icebreaker-fpga/icebreaker/hardware/bitsy-v1.0a/img/bare-ortho-bot_v1.0a.png

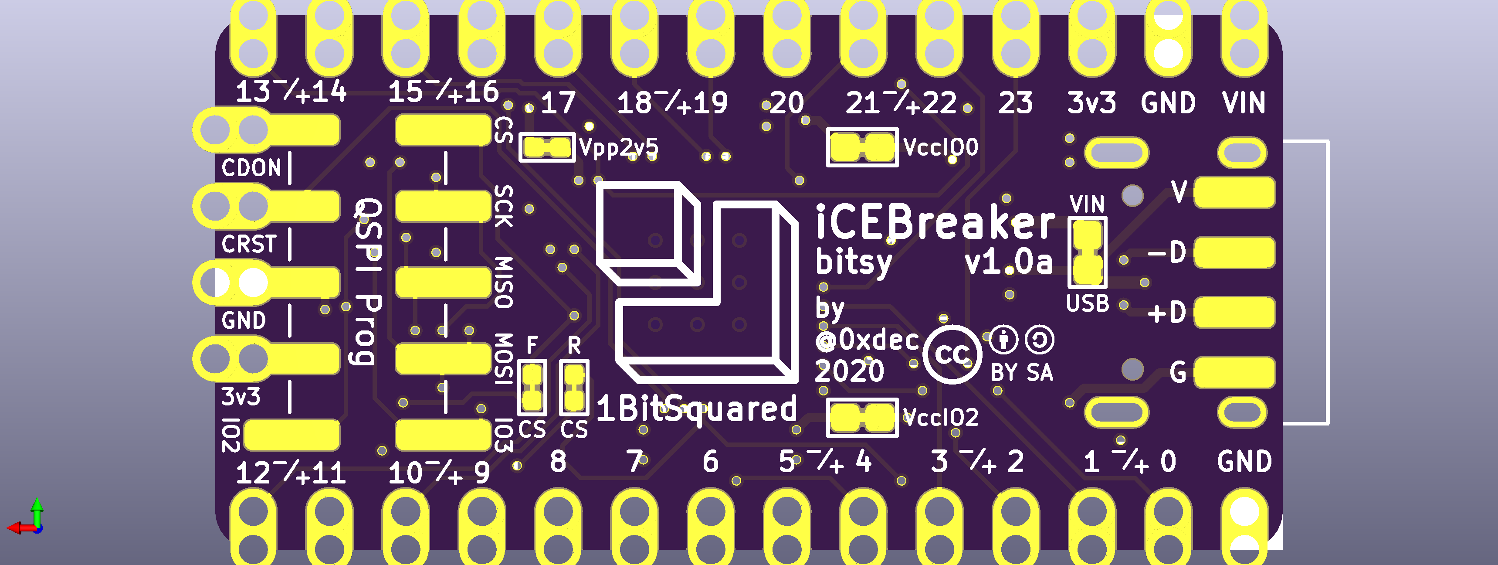
hardware/bitsy-v1.0a/img/bare-ortho-bot_v1.0a.png
