icebreaker-fpga/icebreaker/hardware/bitsy-v1.0a/img/bare-ortho-top_v1.0a.png

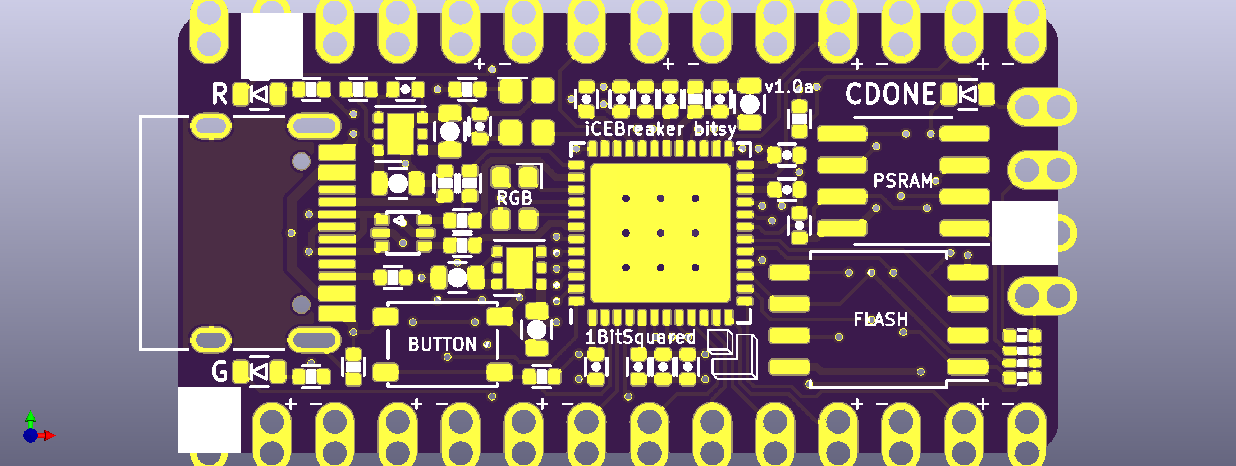
hardware/bitsy-v1.0a/img/bare-ortho-top_v1.0a.png
