icebreaker-fpga/icebreaker/hardware/bitsy-v1.1a/img/bitsy-v1.1a-info-card-top.png

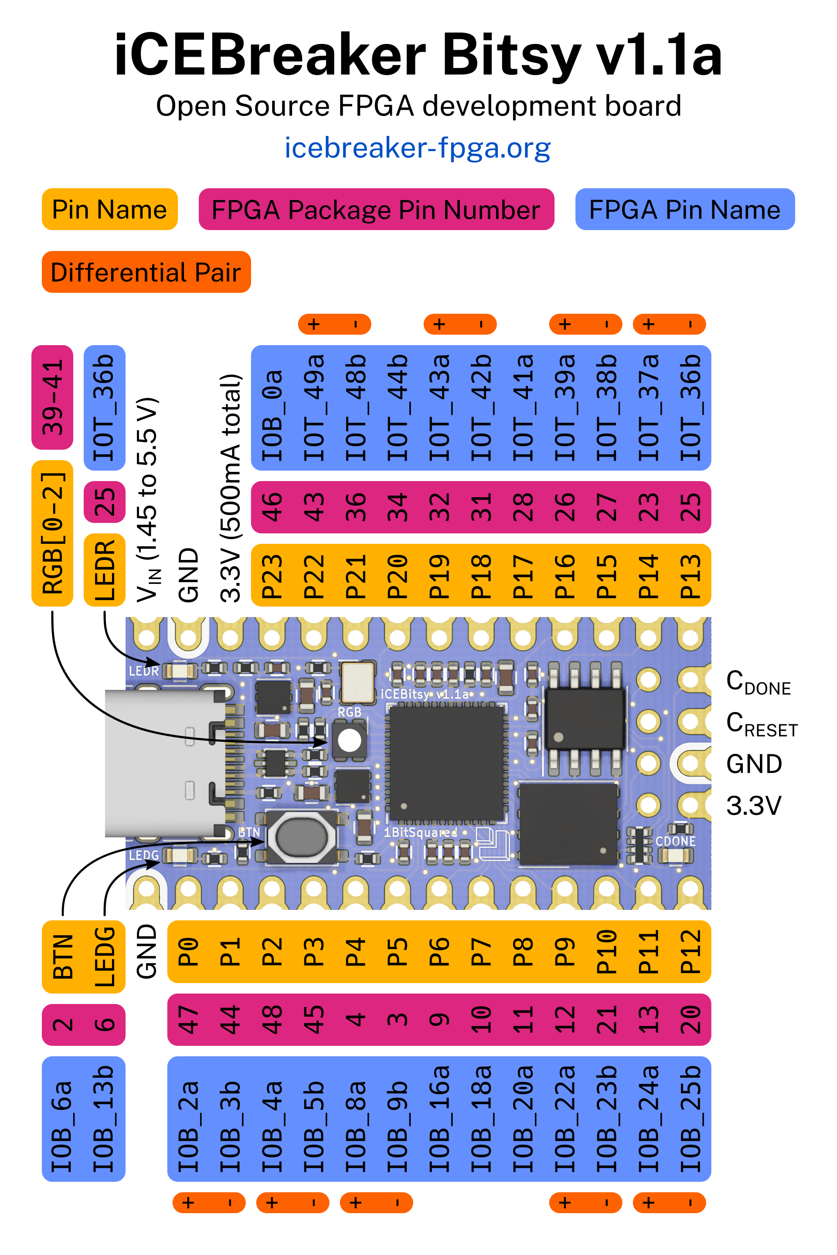
hardware/bitsy-v1.1a/img/bitsy-v1.1a-info-card-top.png
