icebreaker-fpga/icebreaker/hardware/bitsy-v1.1a/img/bitsy-v1.1a-render-ortho-bot.png

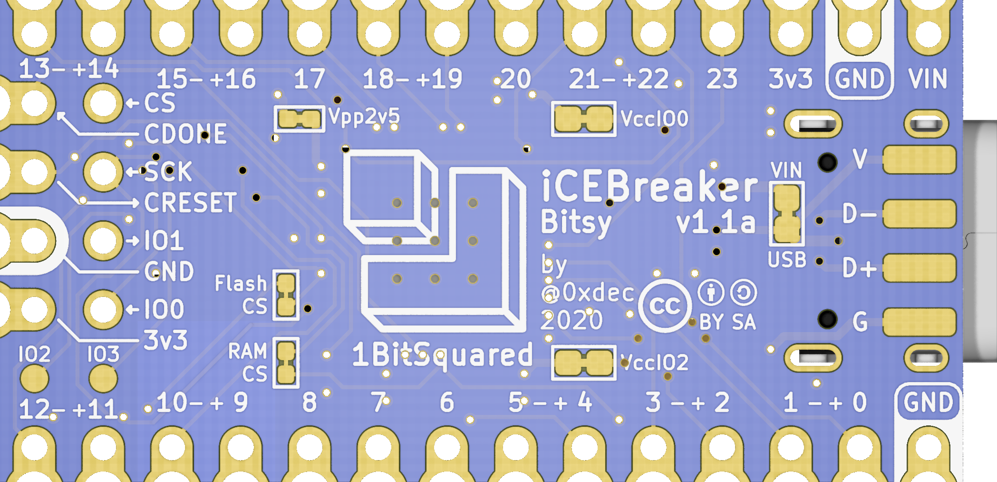
hardware/bitsy-v1.1a/img/bitsy-v1.1a-render-ortho-bot.png
