icebreaker-fpga/icebreaker/hardware/bitsy-v1.1a/img/bitsy-v1.1a-render-ortho-top.png

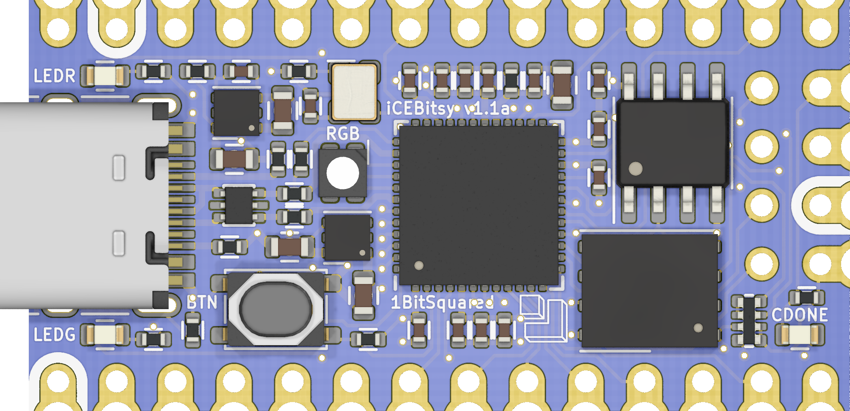
hardware/bitsy-v1.1a/img/bitsy-v1.1a-render-ortho-top.png
