icebreaker-fpga/icebreaker/hardware/bitsy-v1.1b/img/bitsy-v1.1b_info-card_front.png

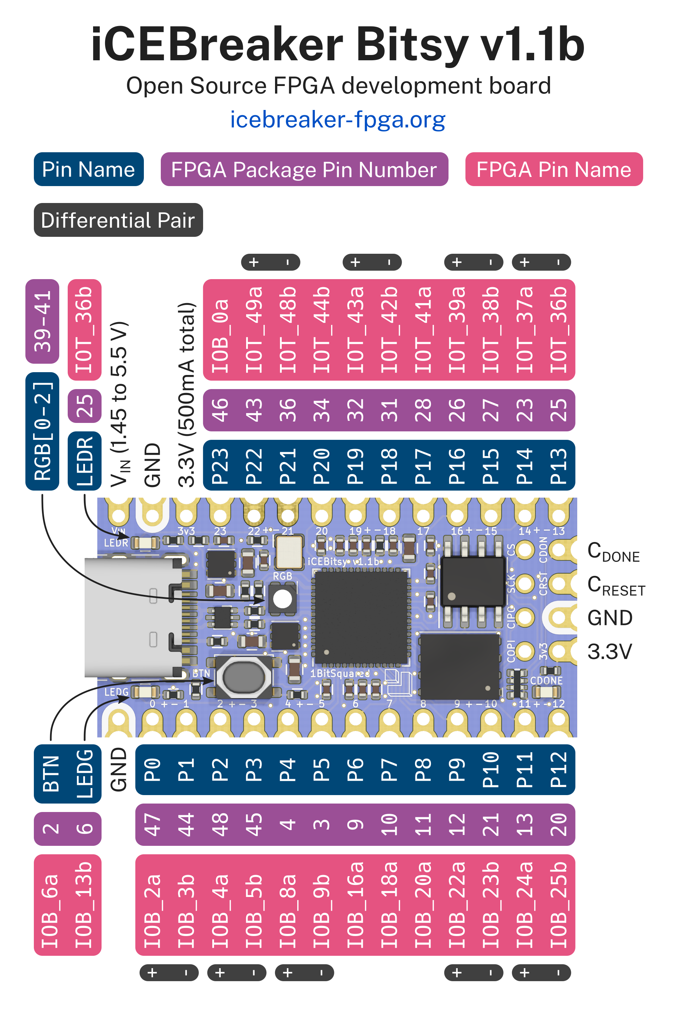
hardware/bitsy-v1.1b/img/bitsy-v1.1b_info-card_front.png
