icebreaker-fpga/icebreaker/hardware/bitsy-v1.1c/ref/icebreaker-bitsy-v1.1c_render_back.png

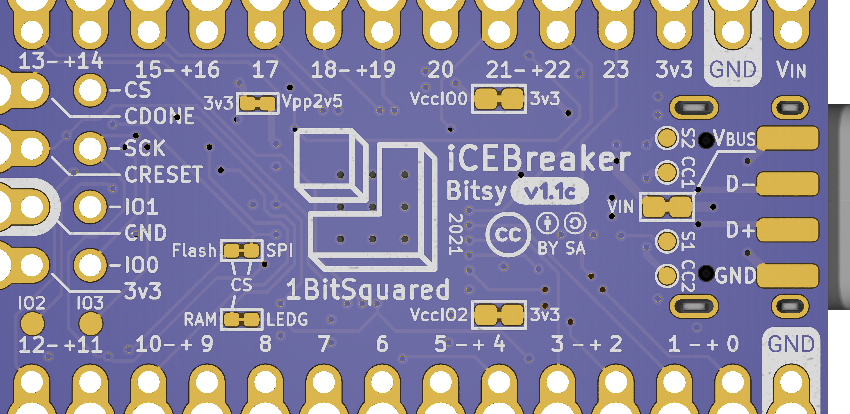
hardware/bitsy-v1.1c/ref/icebreaker-bitsy-v1.1c_render_back.png
