icebreaker-fpga/icebreaker/img/icebreaker-v1_0a-legend.jpg

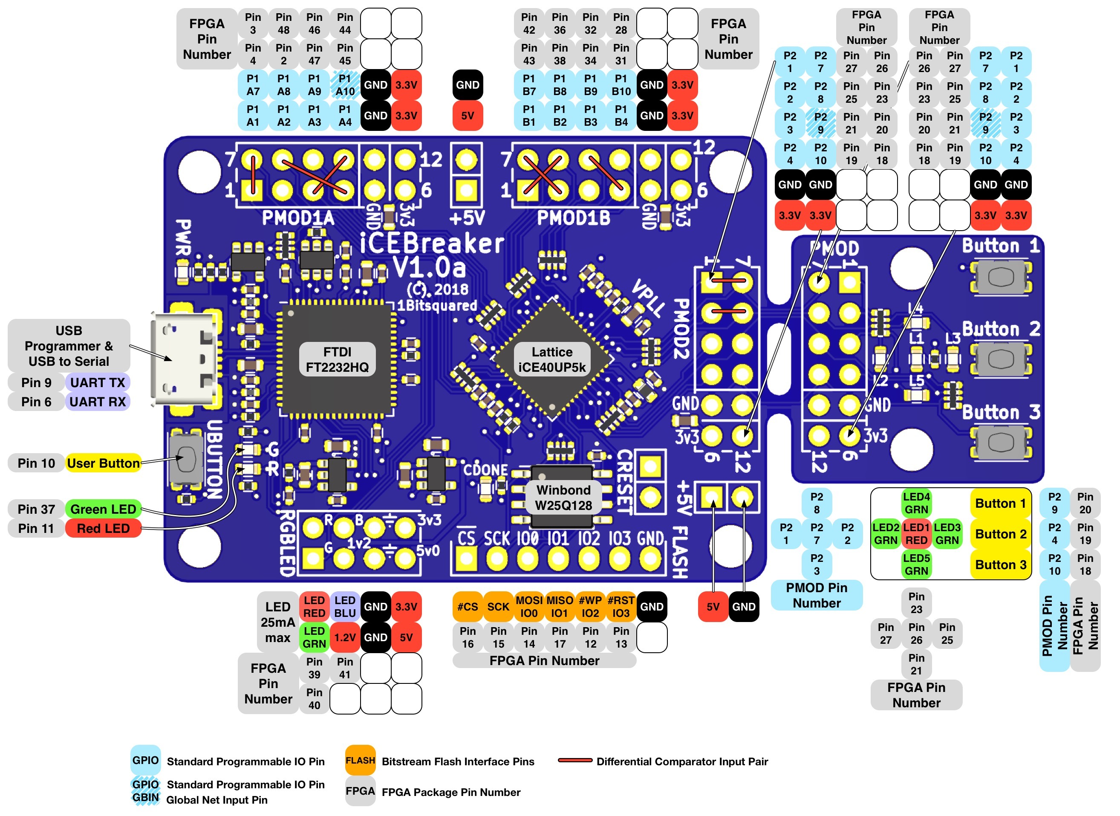
img/icebreaker-v1_0a-legend.jpg
