icebreaker-fpga/icebreaker/hardware/bitsy-v0.1a/icebreaker-bitsy-pinout.pdf

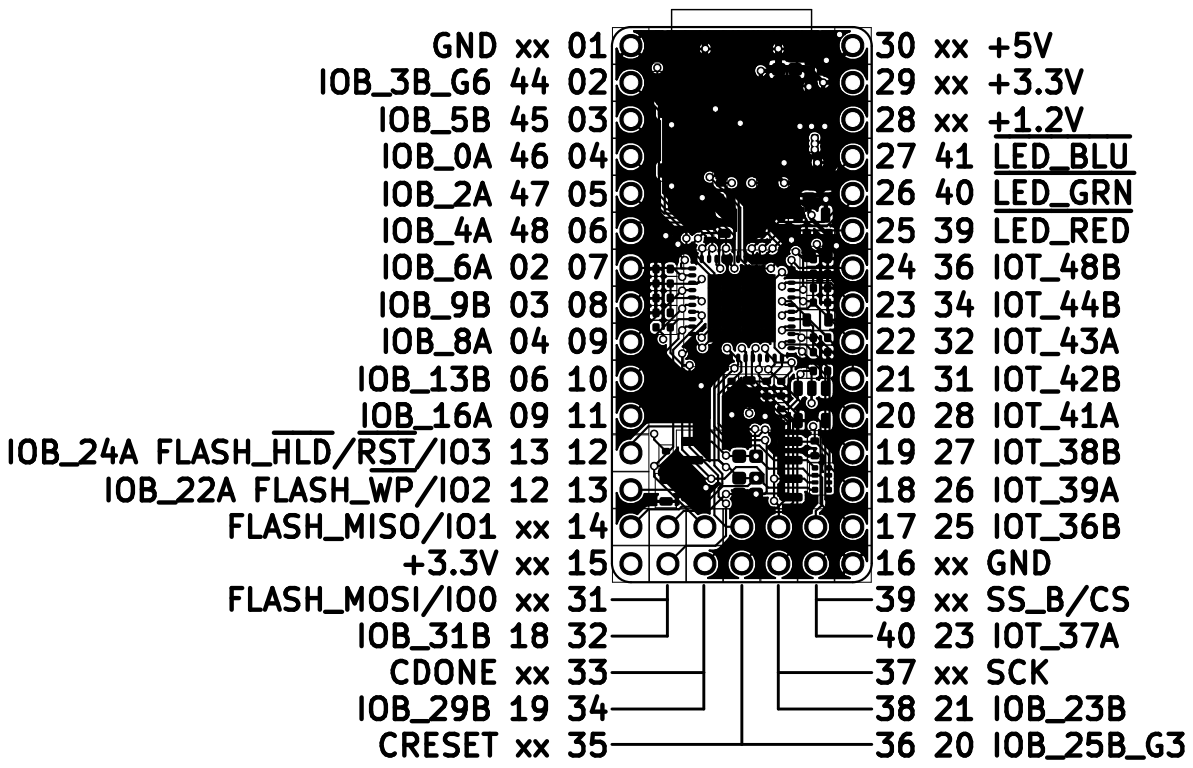
[picture p53: page 1]
